cfp8smataArg/overlord_modificada/assets/img/board_original.jpg

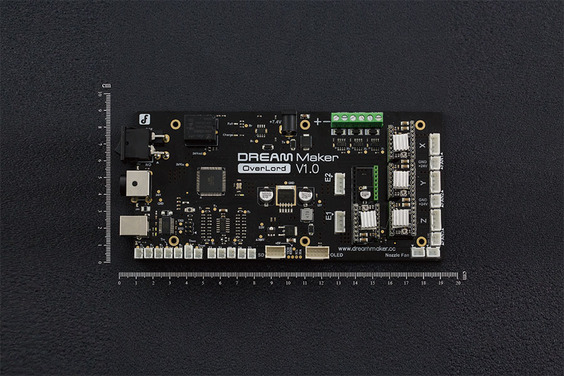
assets/img/board_original.jpg
