cfp8smataArg/overlord_modificada/assets/img/MKS_GenLv1_conexionado.jpg

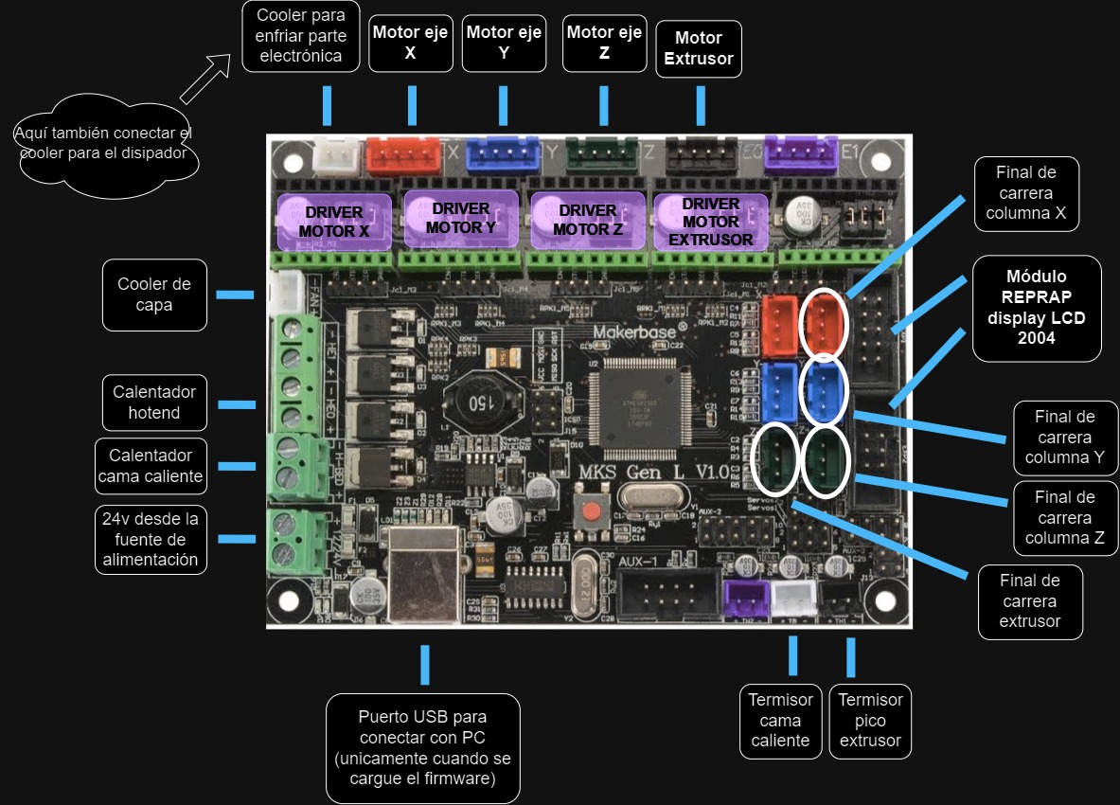
assets/img/MKS_GenLv1_conexionado.jpg
