cfp8smataArg/overlord_modificada/assets/img/MKS_TiynBee_conexionado.jpg

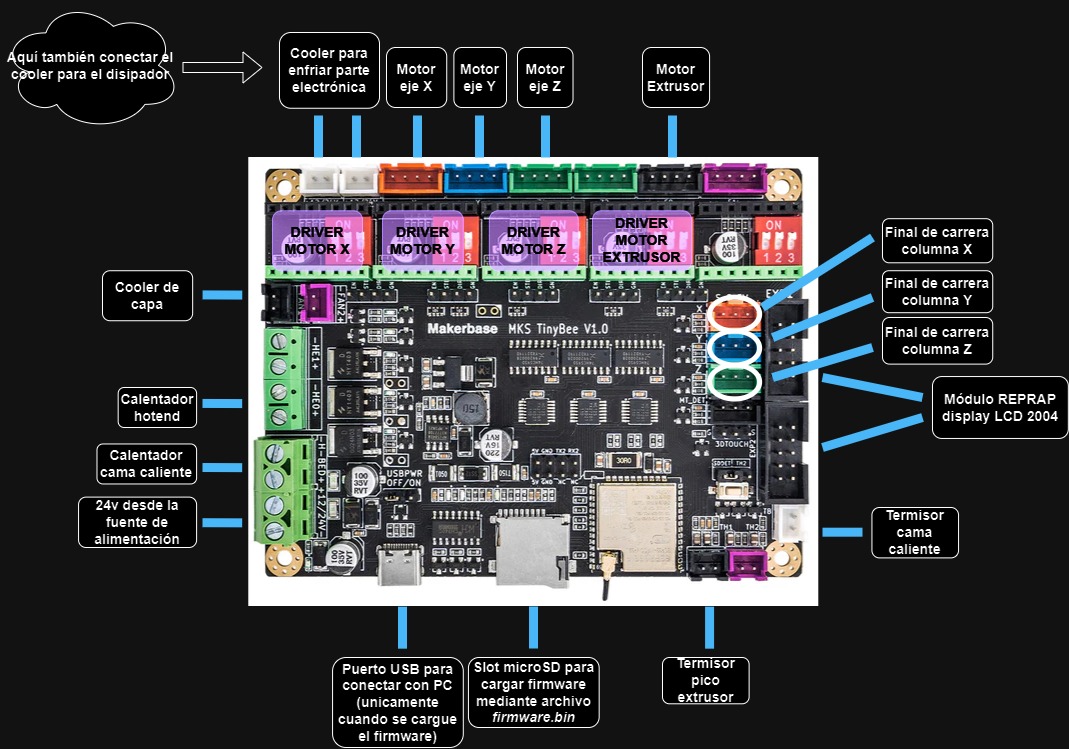
assets/img/MKS_TiynBee_conexionado.jpg
