cfp8smataArg/overlord_modificada/assets/img/panel_lateral.jpg

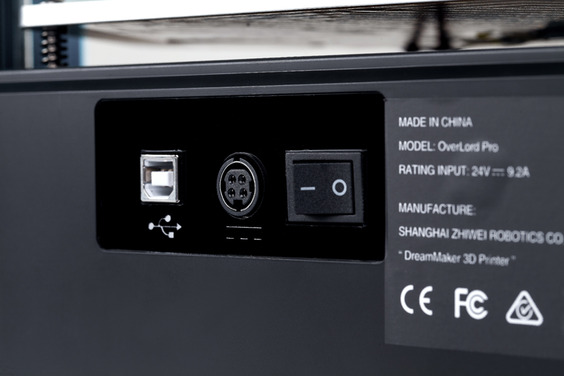
assets/img/panel_lateral.jpg
