cfp8smataArg/overlord_modificada/assets/img/platformio2.jpg

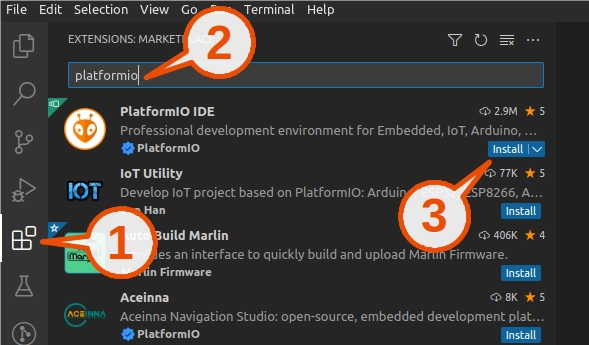
assets/img/platformio2.jpg
