cfp8smataArg/overlord_modificada/assets/img/platformio.jpg

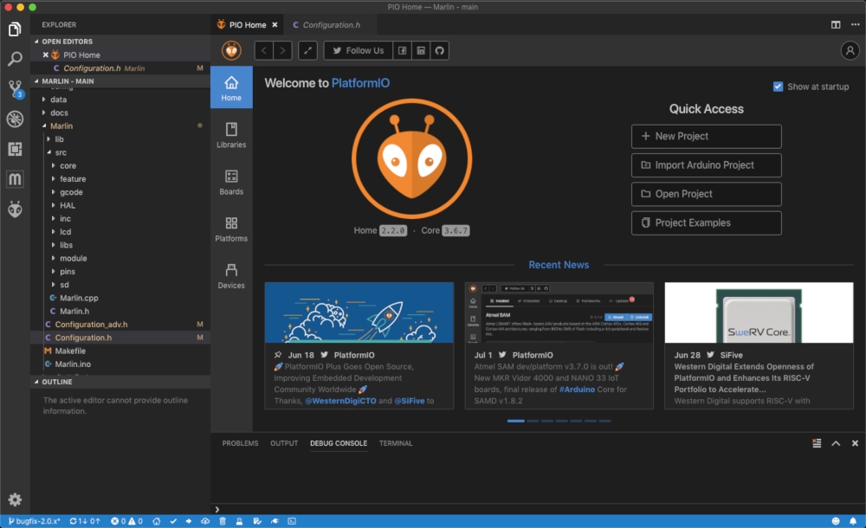
assets/img/platformio.jpg
