cfp8smataArg/overlord_modificada/assets/img/vsc3.jpg

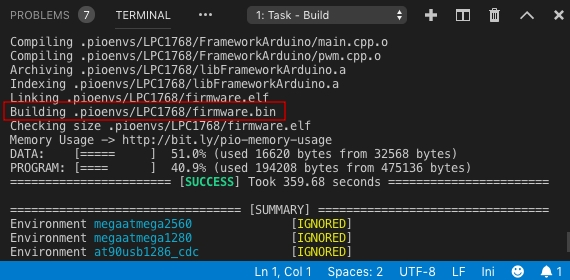
assets/img/vsc3.jpg
